Olsn-Dev/OpenScope/src/clubs.cpp

#include "clubs.h"

const Club CLUBS[NUM_CLUBS] = {
    { "Driver", "D",   1.35f, 0.10f, 12.0f },
    { "3-Wood", "3W",  1.20f, 0.08f, 13.0f },
    { "5-Wood", "5W",  1.10f, 0.08f, 14.0f },
    { "3-Iron", "3I",  0.95f, 0.05f, 16.0f },
    { "4-Iron", "4I",  0.90f, 0.05f, 17.0f },
    { "5-Iron", "5I",  0.82f, 0.05f, 18.0f },
    { "6-Iron", "6I",  0.75f, 0.04f, 20.0f },
    { "7-Iron", "7I",  0.68f, 0.04f, 21.0f },
    { "8-Iron", "8I",  0.60f, 0.03f, 23.0f },
    { "9-Iron", "9I",  0.52f, 0.02f, 25.0f },
    { "PW",     "PW",  0.45f, 0.02f, 28.0f },
    { "GW",     "GW",  0.40f, 0.01f, 32.0f },
    { "SW",     "SW",  0.35f, 0.01f, 35.0f },
    { "LW",     "LW",  0.30f, 0.01f, 40.0f },
};
